eshazen/keyboards/Case/case1/case_left.3mf

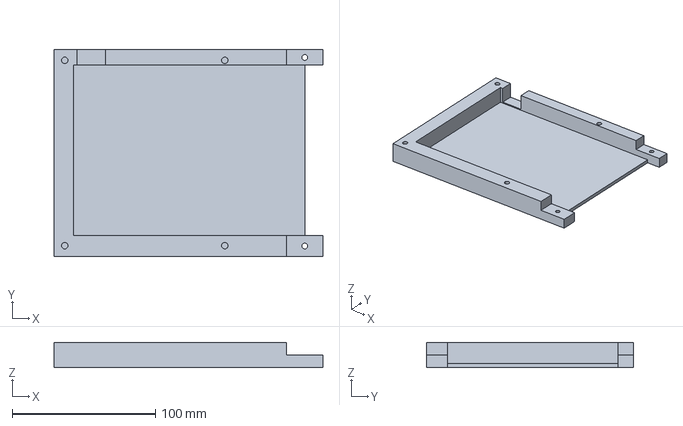
[picture p16: CAD file, 2025-03-27]
Case/case1/case_left.3mf
187.6 x 144.3 x 17.6 mm
