eshazen/keyboards/Case/case1/case_right.3mf

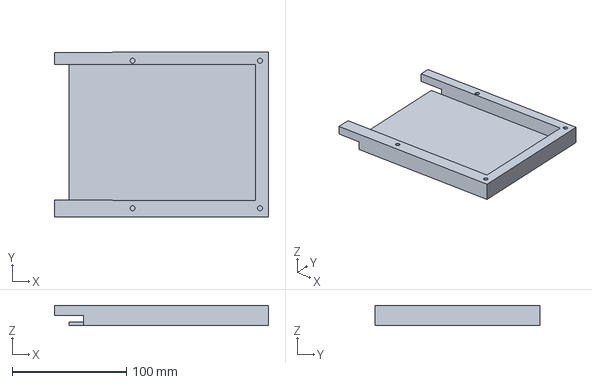
[picture p17: CAD file, 2025-03-23]
Case/case1/case_right.3mf
187.6 x 144.3 x 17.6 mm
