eshazen/keyboards/Case/case1/plate_test.3mf

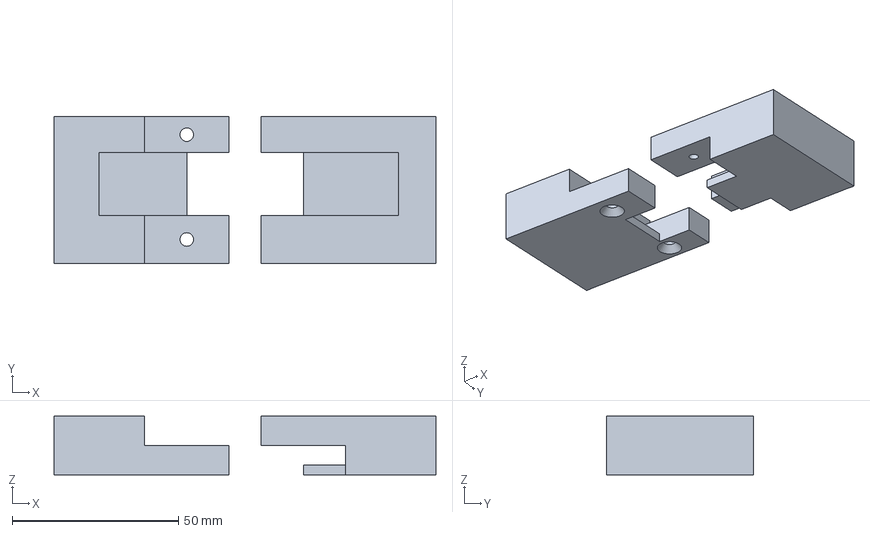
[picture p18: CAD file, 2025-03-12]
Case/case1/plate_test.3mf
114.8 x 44.3 x 17.6 mm
