eshazen/keyboards/Case/case1/test_left.3mf

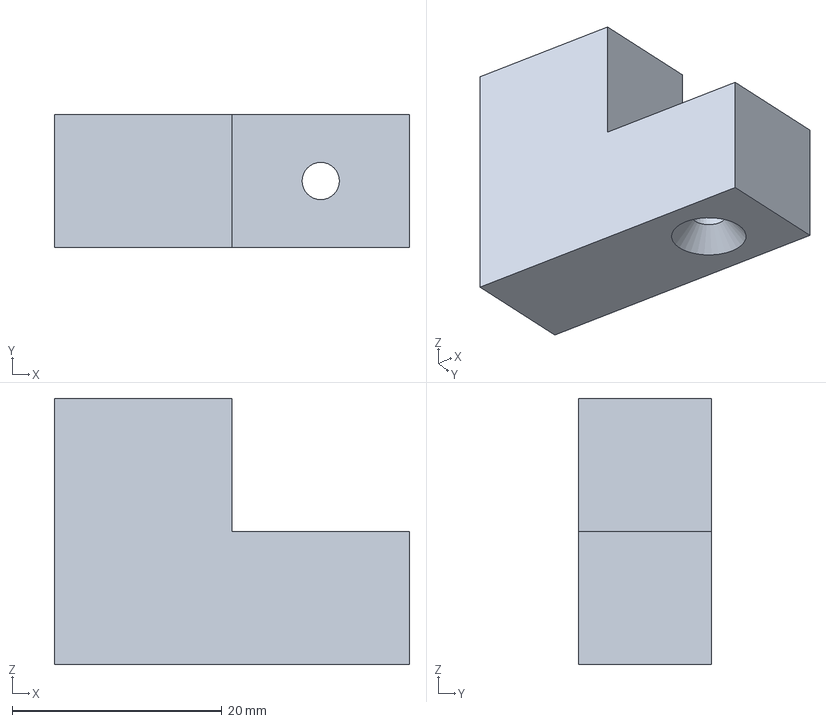
[picture p19: CAD file, 2025-03-12]
Case/case1/test_left.3mf
33.9 x 12.7 x 25.4 mm
