eshazen/keyboards/Case/case1/closed.dxf

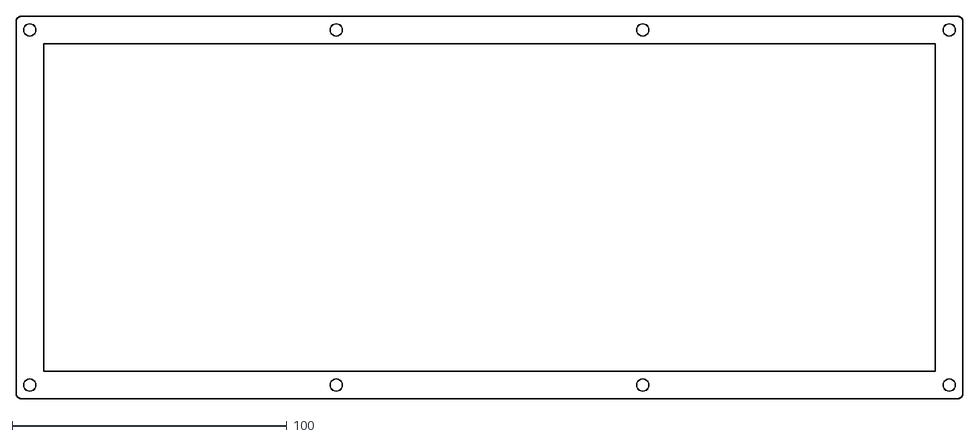
[picture p20: CAD file, 2025-03-10]
Case/case1/closed.dxf
344.8 x 139.3
