eshazen/keyboards/Case/case1/bottom.dxf

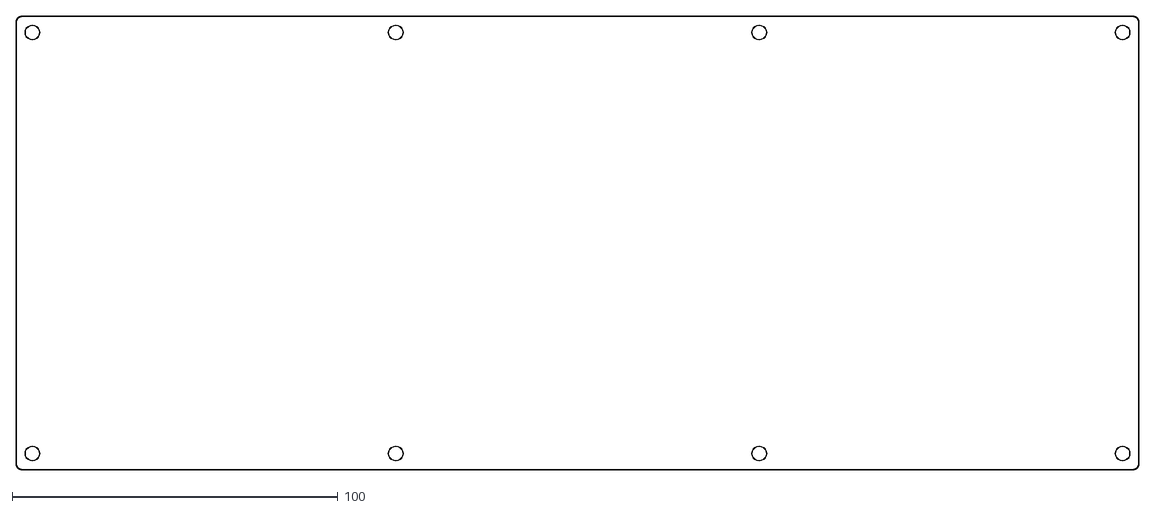
[picture p21: CAD file, 2025-03-10]
Case/case1/bottom.dxf
344.8 x 139.3
