eshazen/keyboards/Case/case1/top.dxf

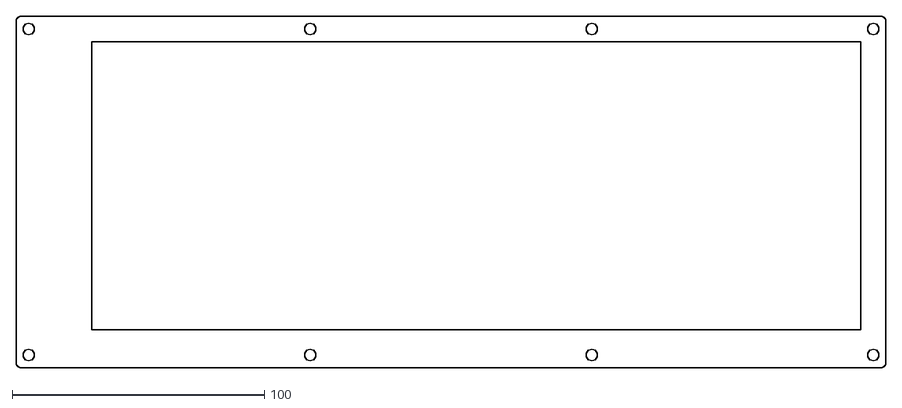
[picture p22: CAD file, 2025-03-10]
Case/case1/top.dxf
344.8 x 139.3
