eshazen/keyboards/Case/case1/plate.step

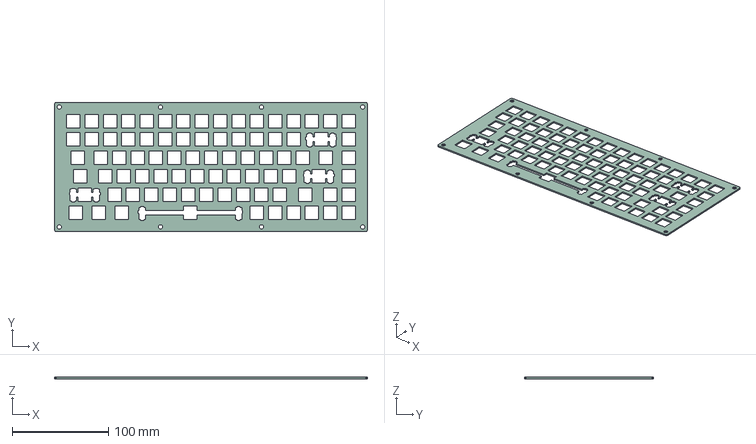
[picture p23: CAD file, 2025-03-10]
Case/case1/plate.step
324.8 x 134.3 x 1.60 mm
