eshazen/keyboards/Case/case1/plate_drawing.dxf

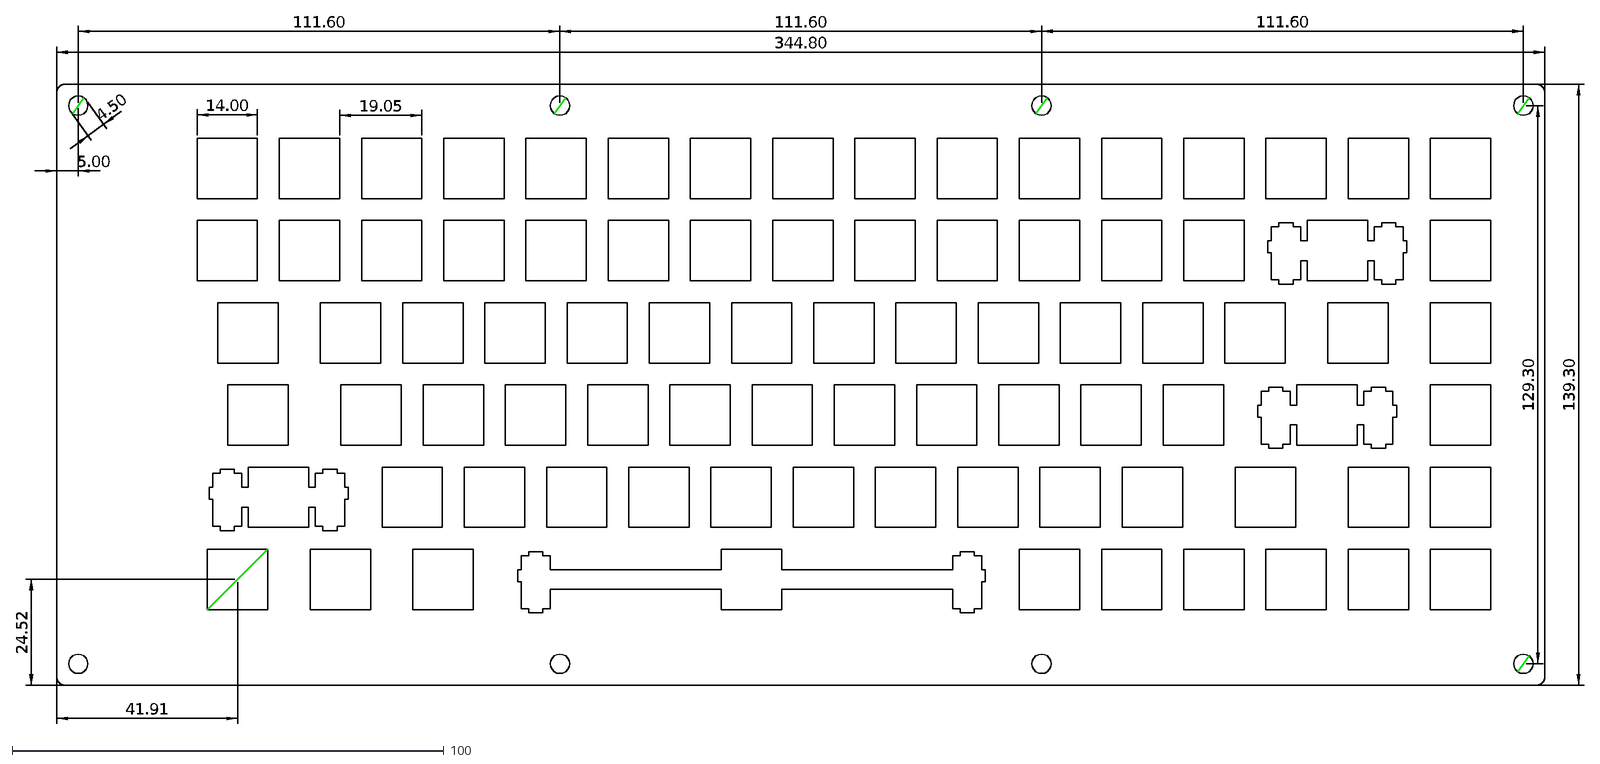
[picture p24: CAD file, 2025-03-10]
Case/case1/plate_drawing.dxf
344.80
139.30
4.50
14.00
19.05
5.00
111.60
129.30
41.91
24.52
