eshazen/keyboards/Case/test.scad

$fn = 32;
mm = 25.4;

wid = 305;
len = 115;

thk = 1*mm;

cube( [wid, len, thk]);
