eshazen/keyboards/portable/trial_stackup.scad

mm = 25.4;
e = 0.1;
$fn = 32;

% translate( [0, 30, 12]) rotate([180, 0, 0]) import("gateron-key-cap.stl");
% import("ks33.stl");
